klay2000/EBike/EBike CAD/Mechanical/Drive Sprocket.iges

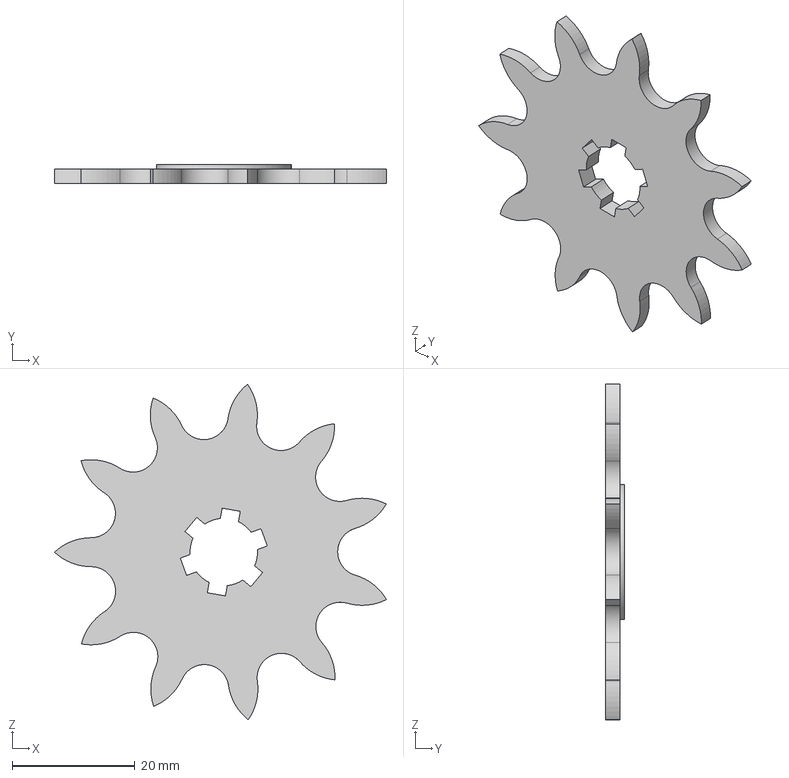
[picture p15: CAD file, 2019-12-17]
EBike CAD/Mechanical/Drive Sprocket.iges
54.1 x 3.18 x 54.7 mm
