klay2000/EBike/EBike_Software/DriveTasks.cpp

#include "DriveTasks.h"
#include <Arduino.h>
#include "AuthTask.h"
#include "Drive.h"
#include "Controls.h"

void DriveTasks::throttleTaskStart(void*){

}

void DriveTasks::throttleTask(void*){
  float amps = 0.0f;
  if(AuthTask::isAuthenticated()) amps = Controls::getInstance()->getThrottle()*(float)Drive::MAX_CURRENT;
  Drive::getInstance()->setAmps(amps);
}
