klay2000/EBike/EBike_Software/AuthTask.cpp

#include "AuthTask.h"
#include <Arduino.h>
#include "Controls.h"
#include "CardReader.h"

String AuthTask::cardUID = "99f6fcb9";

bool AuthTask::cardAuth = false;


bool AuthTask::isAuthenticated(){
  return cardAuth || Controls::getInstance()->getKey();
}

void AuthTask::authTaskStart(void*){}

void AuthTask::authTaskRun(void*){
  
  if(Controls::getInstance()->getKey()){ //kill cardauth if keyauth
    cardAuth = false;
    return;
  }

 if(!CardReader::getInstance()->isNewCard()) return;

 if(!CardReader::getInstance()->readCard()) return;
     
 if(CardReader::getInstance()->cardUID().equals(cardUID)) cardAuth = !cardAuth;



}
