klay2000/EBike/EBike_Software/CardReader.h

#ifndef CARDREADER
#define CARDREADER

#include <MFRC522.h>

#include "string.h"

class CardReader{
  
  private:
  const int MFRC_CS_PIN = 14;

  MFRC522* mfrc;

  static CardReader* instance;
  CardReader();

  public:
  static CardReader* getInstance();
    
  bool isNewCard();
  bool readCard();
  String cardUID();
};

#endif
