klay2000/EBike/EBike_Software/Scheduler.h

#ifndef SCHEDULER
#define SCHEDULER

#define MAX_TASKS 10

struct Task
{

  unsigned long interval;

  void (*launch)(void*);
  void (*repeat)(void*);

  Task(void l(void*), void r(void*), unsigned long i);
};

class Scheduler
{
private:
  Task *tasks[MAX_TASKS];

  unsigned long taskRunTimes[MAX_TASKS];

  int currentTask = 0;
  int numOfTasks = 0;

  static Scheduler *instance;
  Scheduler();

public:
  static Scheduler *getInstance();

  void addTask(Task *task);

  void tick();
};

#endif
